mpph21/Proyecto-Byul/b-max.jpg

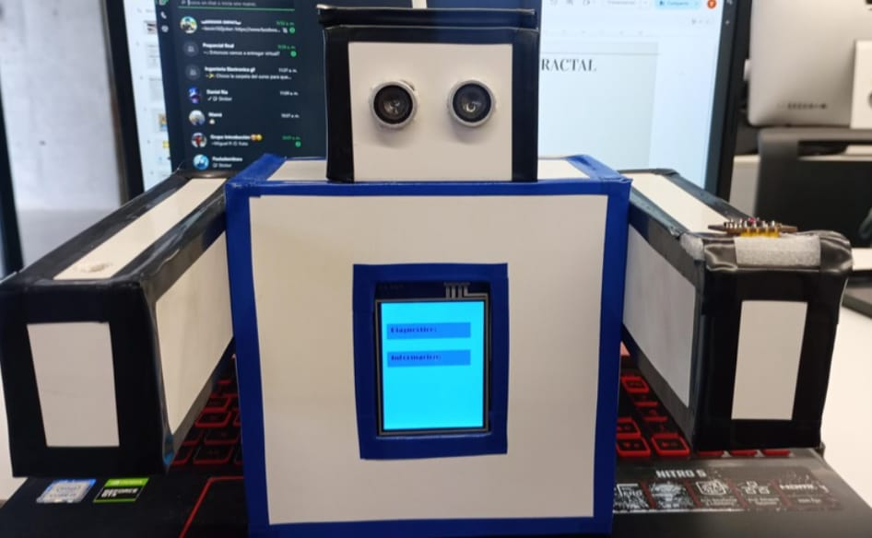
b-max.jpg
