mpph21/Proyecto-Byul/cronograma.png

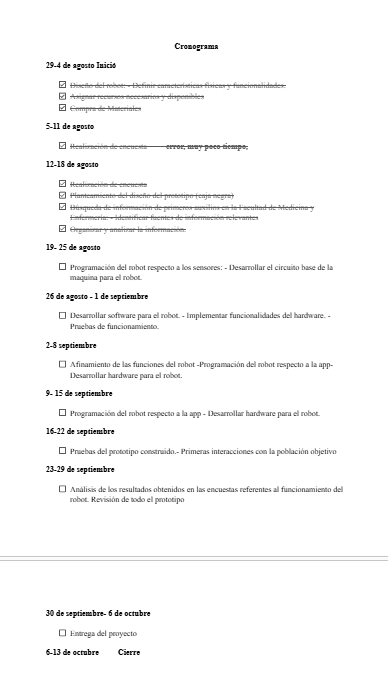
cronograma.png
