mpph21/Proyecto-Byul/diagrama .png

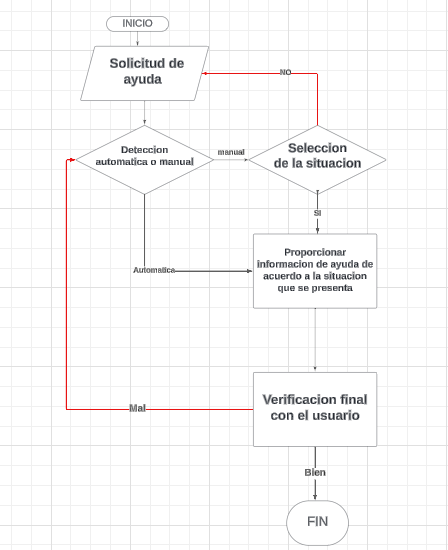
diagrama .png
