mpph21/Proyecto-Byul/Diagrama de interacion .png

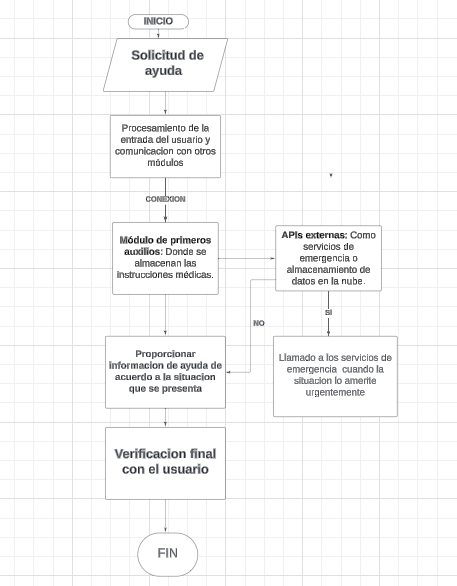
Diagrama de interacion .png
