mpph21/Proyecto-Byul/diagrama_de_caja_negra.jpg

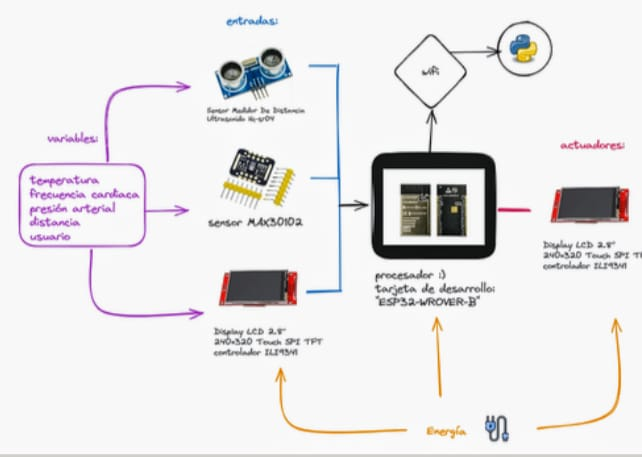
diagrama_de_caja_negra.jpg
