mpph21/Proyecto-Byul/interconectados.jpg

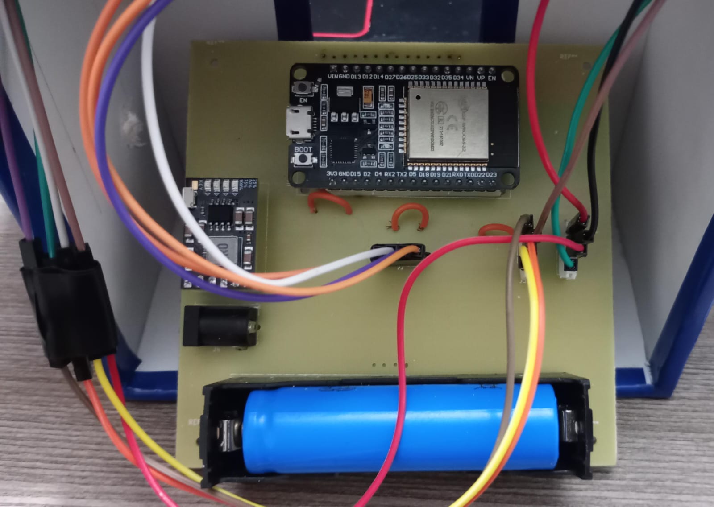
interconectados.jpg
