mpph21/Proyecto-Byul/pantallaLCD. .jpg

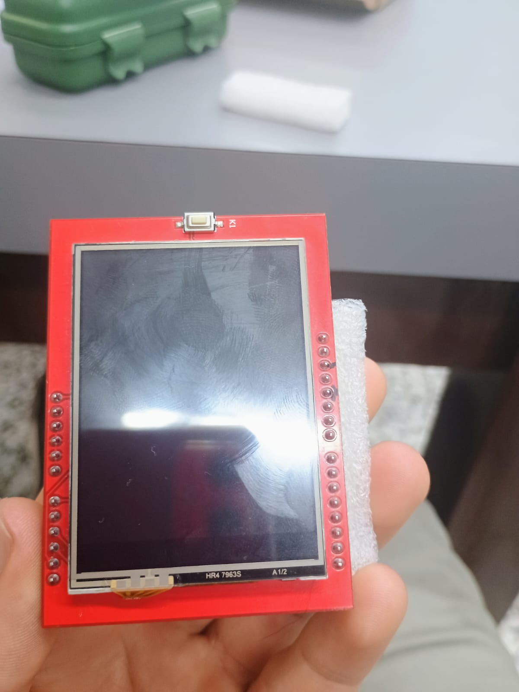
pantallaLCD. .jpg
