mpph21/Proyecto-Byul/pcbByul/Imagen de WhatsApp 2024-09-24 a las 17.16.44_98278a7d.jpg

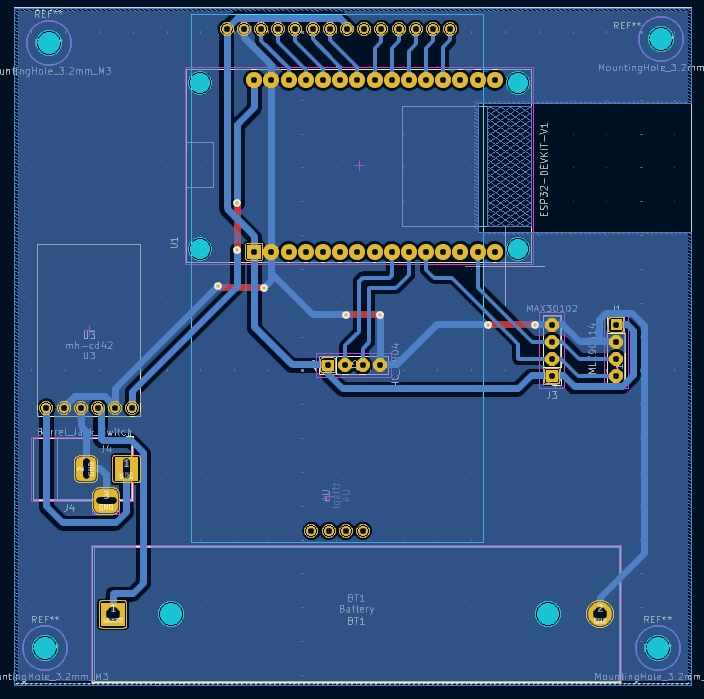
pcbByul/Imagen de WhatsApp 2024-09-24 a las 17.16.44_98278a7d.jpg
