mpph21/Proyecto-Byul/pcbByul/Imagen de WhatsApp 2024-09-24 a las 17.17.50_aacd6478.jpg

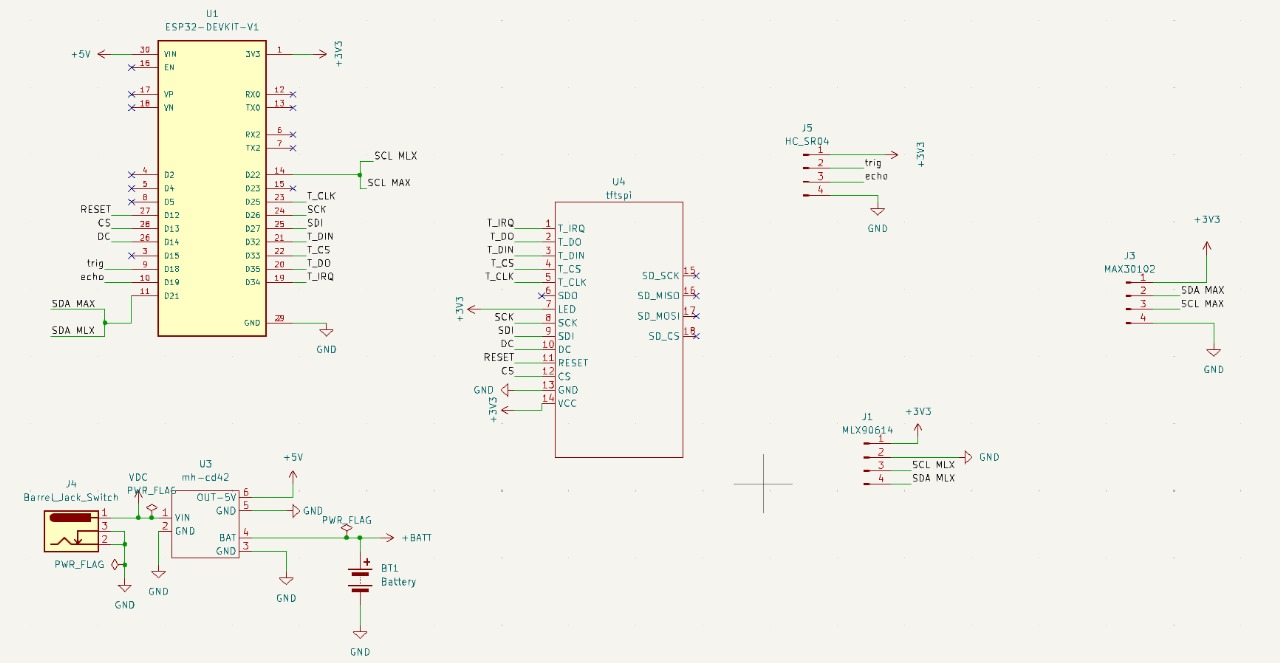
pcbByul/Imagen de WhatsApp 2024-09-24 a las 17.17.50_aacd6478.jpg
