mpph21/Proyecto-Byul/pcbByul/Imagen de WhatsApp 2024-09-24 a las 17.18.33_b2b94559.jpg

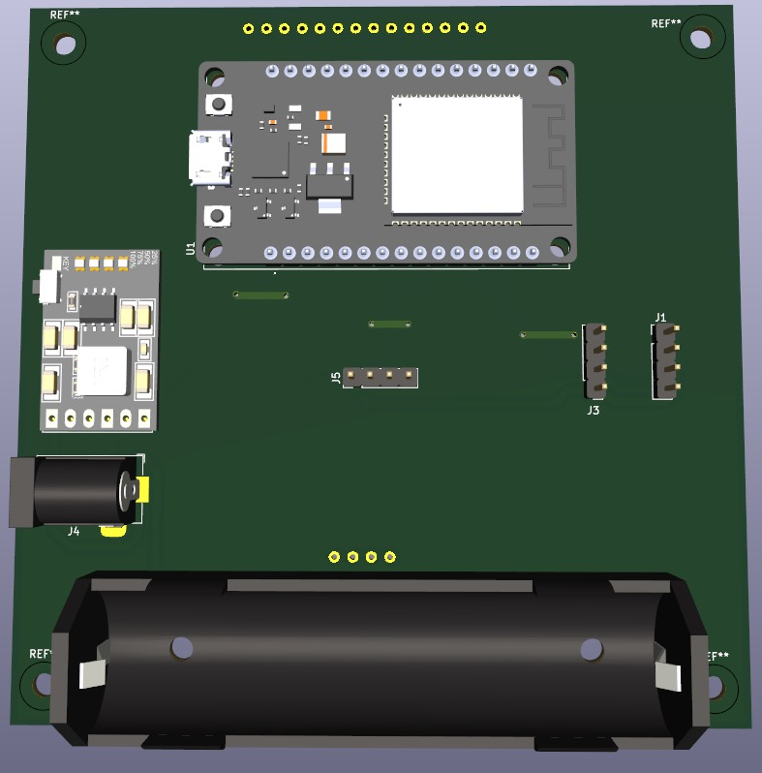
pcbByul/Imagen de WhatsApp 2024-09-24 a las 17.18.33_b2b94559.jpg
