mpph21/Proyecto-Byul/pcbByul/Imagen de WhatsApp 2024-09-24 a las 17.18.48_08502464.jpg

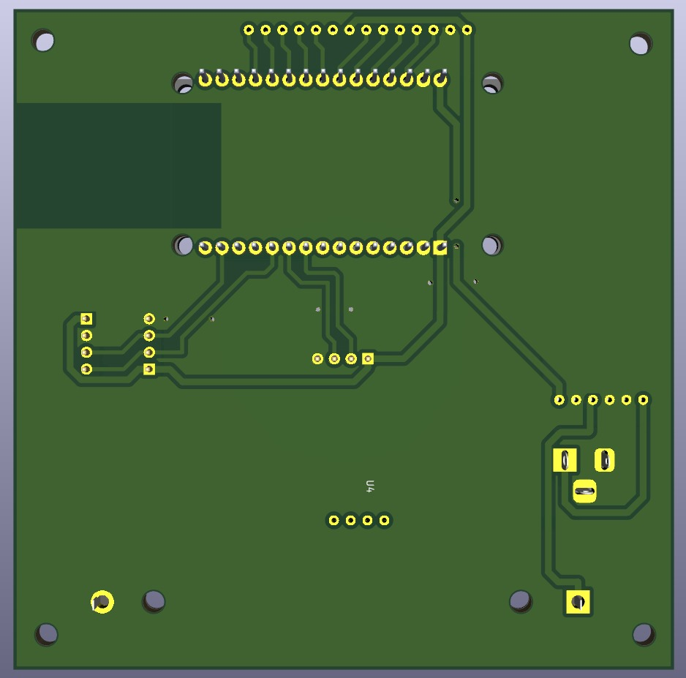
pcbByul/Imagen de WhatsApp 2024-09-24 a las 17.18.48_08502464.jpg
