mpph21/Proyecto-Byul/Planeación Byul/Diagrama_projecto_nacho.png

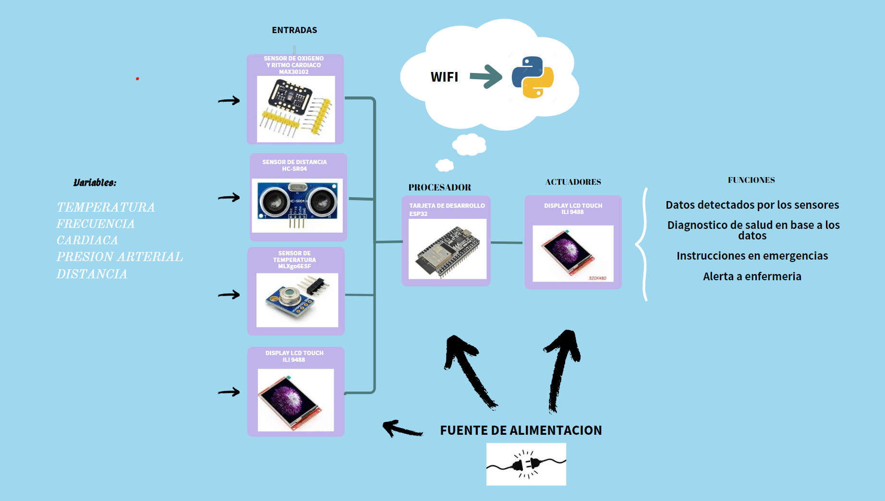
Planeación Byul/Diagrama_projecto_nacho.png
