mpph21/Proyecto-Byul/robot.jpg

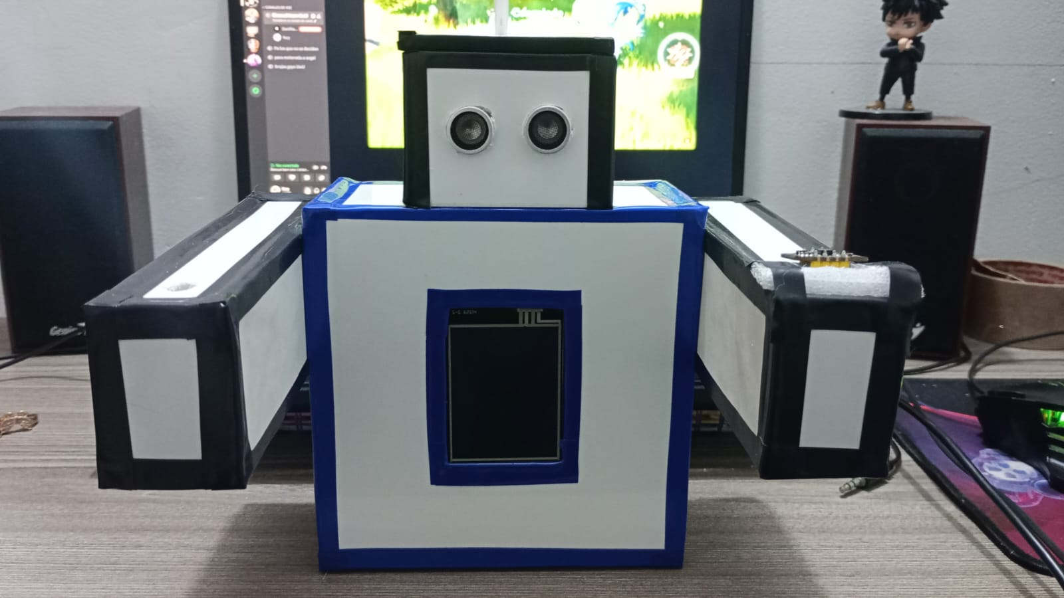
robot.jpg
