mpph21/Proyecto-Byul/Sistemas_subsistemas.jpg

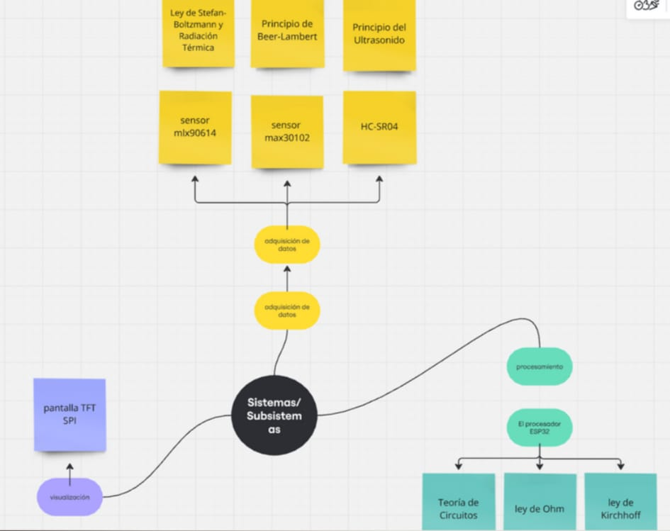
Sistemas_subsistemas.jpg
