mpph21/Proyecto-Byul/Planeación Byul/InvestigacionComponentes/ili9341-module.png

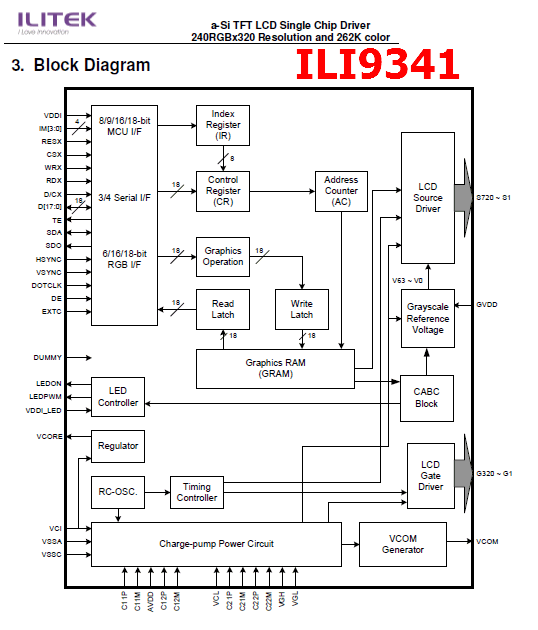
Planeación Byul/InvestigacionComponentes/ili9341-module.png
