mpph21/Proyecto-Byul/Planeación Byul/InvestigacionComponentes/OIP.png

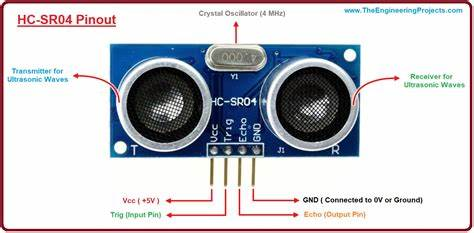
Planeación Byul/InvestigacionComponentes/OIP.png
