mpph21/Proyecto-Byul/Planeación Byul/InvestigacionComponentes/R.png

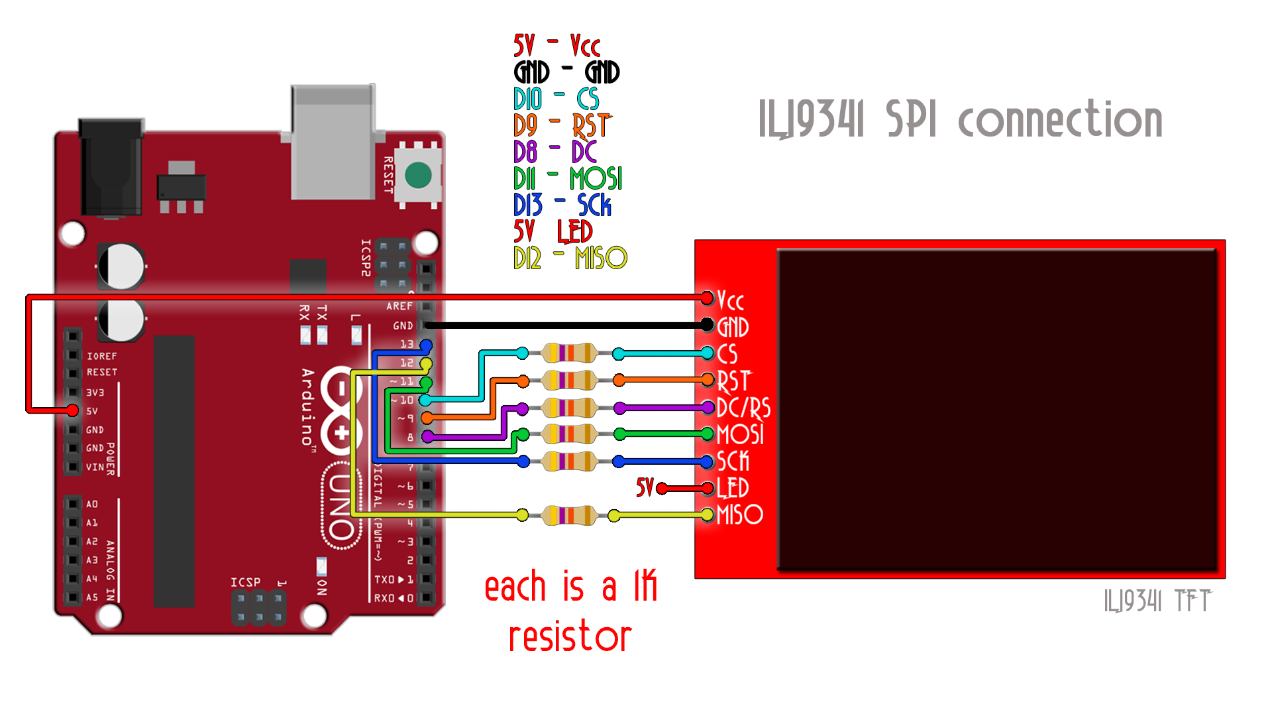
Planeación Byul/InvestigacionComponentes/R.png
