mpph21/Proyecto-Byul/Planeación Byul/InvestigacionComponentes/arduino_max30102_wiring.png

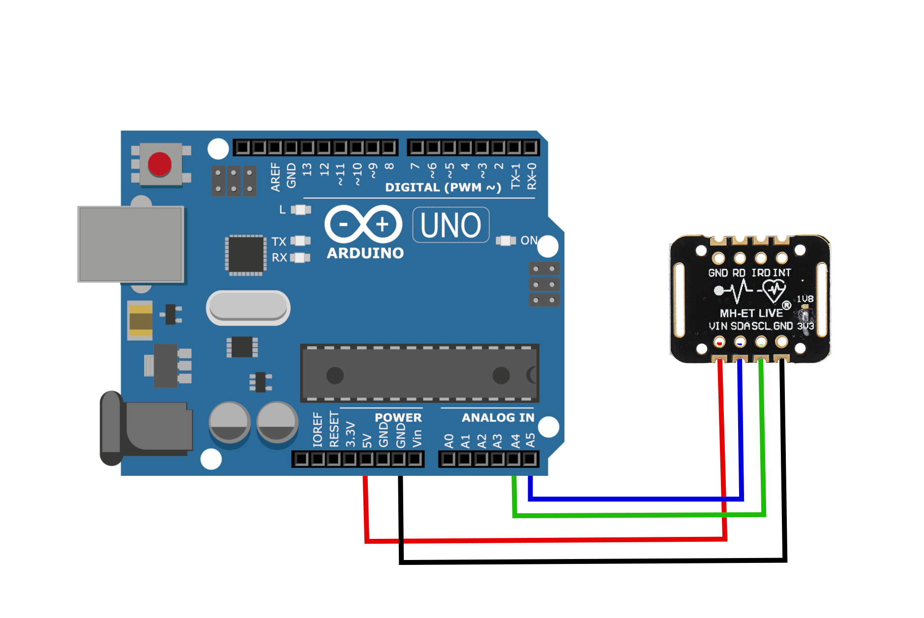
Planeación Byul/InvestigacionComponentes/arduino_max30102_wiring.png
