mpph21/Proyecto-Byul/Planeación Byul/InvestigacionComponentes/ESP8266-Ultrasonic-Sensor-Wiring-Fritzing-Diagram.png

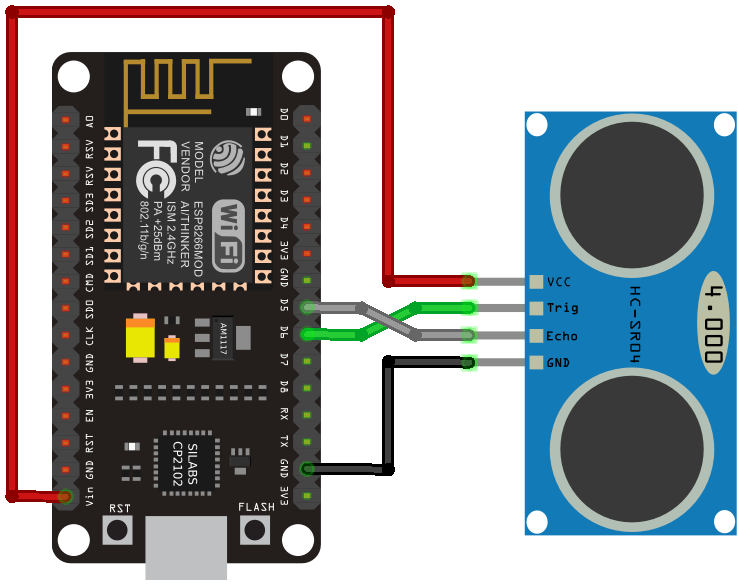
Planeación Byul/InvestigacionComponentes/ESP8266-Ultrasonic-Sensor-Wiring-Fritzing-Diagram.png
