mpph21/Proyecto-Byul/Planeación Byul/InvestigacionComponentes/wiring-diagram.png

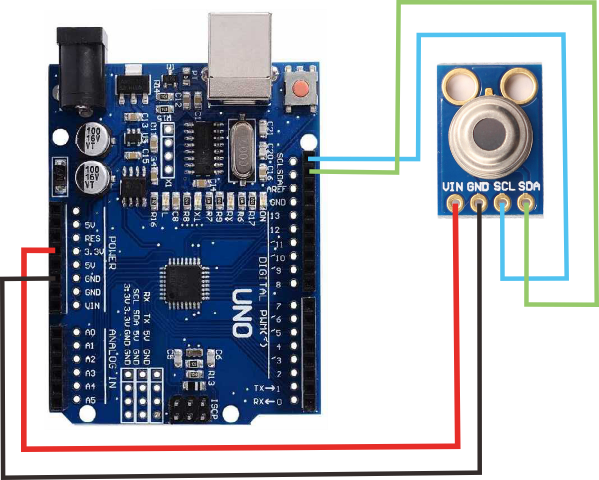
Planeación Byul/InvestigacionComponentes/wiring-diagram.png
