mpph21/Proyecto-Byul/ByulCodigo/codigoFinal/auxInfo.py

steps = [
            "Vendaje de Heridas:\n\nVendas: sirven para inmovilizar extremidades y realizar compresion en caso de hemorragias. Pueden ser elasticas, de tela o de gasa.\n\nHerida: Lesion, normalmente sangrante, que se produce en los tejidos, exteriores del cuerpo.",
            "Paso 1. Coloque un vendaje sobre la herida\n\n - Use guantes u otra proteccion para evitar el contacto con la sangre de la persona afectada.\n\n - Limpie la herida con agua o suero fisiologico.\n\n Coloque una compresa limpia sobre toda la herida. Las compresas de gasa permiten que pase el aire y, de esta manera, la herida sana mas rapido.\n\n- Si la sangre pasa a traves de la compresa, coloque otra compresa sobre la primera.",
            "Paso 2. Cubra el vendaje\n\n- Use un rollo de gasa o tiras de tela para envolver el aposito (material utilizado para cubrir y proteger la herida) y el area alrededor de la herida varias veces.\n\n - Extienda el vendaje por lo menos una pulgada mas a cada lado del aposito.\n\n- No coloque el vendaje tan apretado que interfiera con la circulacion de la sangre a los tejidos sanos.",
            "Paso 3. Asegure el vendaje\n\n- Coloque una cinta adhesiva sobre el vendaje.\n\n- No asegure el vendaje tan apretado que el color de los dedos de las manos o de los pies se vuelve palido o azul.",
            "Paso 4. Examine la circulacion\n\n- Revise la circulacion en el area debajo del vendaje despues de varios minutos y una vez mas despues de varias horas. Si la circulacion no es buena, la piel puede verse palida o de color azul o puede sentirse fria. Los signos de una mala circulacion tambien incluyen adormecimiento y hormigueo.\n\n- Si la circulacion se redujo, afloje el vendaje de inmediato. Si los sintomas persisten, solicite atencion medica.",
            "Que no hacer:\n\n- Nunca frotar la herida para quitar la suciedad."
        ]
emergency_steps = [
            "Numeros de Emergencia:\n\nLinea 125/123 - Bogota\n\nLinea telefonica gratuita atendida por la Secretaria Distrital de Salud de Bogota, creada para responder de forma inmediata a las urgencias, emergencias y desastres relacionados con atencion en salud que ocurran en la ciudad.",
            "La linea 125/123 es manejada por personas entrenadas con espiritu de ayuda, amabilidad y cortesia, que entienden la situacion y la saben manejar. Estan capacitadas para dar una respuesta especializada e inmediata a cada solicitud.",
            "!Salve una vida, llame al 125/123!\n\nAl llamar a la linea de emergencias 125/123, proporcione la siguiente informacion precisa:\n\n1. Nombre\n2. El numero del telefono de donde esta llamando\n3. El lugar del evento: direccion correcta y orientaciones para que se pueda llegar rapidamente",
            "4. Que pasa: numero de personas afectadas, tipo de incidente y si hay alguna persona capacitada que este prestando ayuda\n5. La hora en que se presento el incidente"
        ]
        
hemorrhage_steps = [
            "Control de hemorragias:\n\na. Informacion general: Ciertas heridas, cortes, desgarros y otras lesiones pueden causar un sangrado intenso. Una persona que tiene un sangrado incontrolable puede morir en cinco minutos, por lo que es importante detener rapidamente la perdida de sangre.",
            "b. Tratamiento. En caso de sangrado intenso, toma estas medidas de primeros auxilios:\n\n1. Antes de buscar donde se encuentra la herida, ponte guantes desechables y equipo de proteccion personal, si lo tienes.\n\n2. Quita cualquier tipo de ropa o suciedad sobre la herida. Busca el origen del sangrado. Es posible que la persona haya sufrido mas de una lesion. Quita cualquier suciedad evidente de la herida, pero no intentes limpiarla.",
            "3. Deten el sangrado. Cubre la herida con una gasa esteril o un paño limpio. Presiona firmemente con la palma de la mano hasta que deje de sangrar. Envuelve la herida con una venda gruesa o un pano limpio y cinta adhesiva. Eleva la zona de la herida por encima de la altura del corazon, en la medida de lo posible.",
            "4. Ayuda a la persona herida a recostarse. Si es posible, coloca a la persona sobre una alfombra o una manta para evitar que pierda calor corporal. Eleva los pies si notas signos de estado de choque, como debilidad, piel seca y sudorosa o pulso acelerado. Tranquiliza a la persona herida.",
            "5. Coloca mas vendas si es necesario. Si la sangre se filtra a traves de la venda, coloca mas gasa o panos encima. Luego, sigue presionando con firmeza la zona.",
            "6. Torniquetes: un torniquete controla eficazmente un sangrado en una extremidad que pone en riesgo la vida. De ser necesario, aplica un torniquete comprado, si lo tienes y sabes como usarlo. Cuando llegue el personal de ayuda, informales el tiempo que lleva colocado el torniquete.",
            "7. Manten a la persona inmovil. Si estas esperando a que llegue el personal de ayuda, intenta que la persona herida no se mueva. Si no has llamado al personal de ayuda, lleva a la persona a la sala de emergencias lo antes posible.",
            "8. Lavate las manos. Despues de ayudar a la persona herida, lavate las manos, aunque no parezca que te hayas manchado con sangre.",
            "c. Que evitar:\n\n1. No quites objetos grandes o que esten muy incrustados.\n2. No explores la herida.\n3. No apliques presion sobre una lesion en el ojo ni un objeto incrustado.\n4. No apliques presion sobre una herida en la cabeza si sospechas que hay una fractura de craneo.\n5. No uses un torniquete improvisado, como una bufanda o un cinturon."
        ]
        
burn_steps = [
            "QUEMADURAS MENORES:\n"
            "Si no hay rupturas en la piel:\n"
            "Deje correr agua fria sobre la zona de la quemadura o sumerja la zona en agua fria (no helada).\n"
            "Mantenga la zona en el agua durante al menos de 5 a 30 minutos. Una toalla limpia, humeda y fria tambien ayuda a reducir el dolor.\n"
            "Calme y reconforte a la persona.\n"
            "Luegodelavar o remojar la quemadura en agua, cubrala con un vendaje esteril y seco o con un aposito limpio.\n"
            "Proteja la quemadura de presiones o fricciones.\n"
            "El ibuprofeno o el paracetamol de venta libre pueden ayudar a aliviar el dolor y la inflamacion. NO le de acido acetilsalicilico (aspirin) a ninos menores de 12 años.\n"
            "Una vez que se enfrie la piel, una locion humectante que contenga aloe y un antibiotico tambien puede ayudar.\n"
            "Las quemaduras menores suelen sanar sin tratamiento adicional.\n"
            "Asegurese que la persona este al dia con la vacuna antitetanica.",

            "QUEMADURAS GRAVES:\n"
            "Si alguien se prende fuego, digale que se detenga, se tire al suelo y ruede.\n"
            "Envuelva a la persona con un material grueso como un abrigo de algodon o lana, una alfombra o una manta.\n"
            "Rocie agua sobre la persona.\n"
            "Cerciorese de que la persona ya no este en contacto con materiales ardientes o humeantes.\n"
            "NO le quite las ropas quemadas que esten pegadas a la piel.\n"
            "Verifique que la persona este respirando. De ser necesario, comience a administrar respiracion artificial y RCP.\n"
            "Cubra la zona de la quemadura con un vendaje esteril y seco o una tela limpia.\n"
            "Si los dedos de las manos o de los pies sufrieron quemaduras, separelos con compresas secas.\n"
            "Eleve la parte del cuerpo quemada por encima del nivel del corazon.\n"
            "NO toque directamente a la victima si una lesion electrica causo la quemadura.",
            
            "Las cosas que NO se deben hacer para las quemaduras incluyen:\n"
            "NO aplique aceite, mantequilla, hielo, medicamentos, cremas, aceites en aerosol ni ningun otro remedio casero en las quemaduras graves.\n"
            "NO respire, sople ni tosa sobre la quemadura.\n"
            "NO toque la piel muerta o ampollada.\n"
            "NO retire la ropa que este pegada a la piel.\n"
            "NO administre nada a la persona por via oral si hay una quemadura grave.\n"
            "NO ponga una quemadura grave en agua fria, pues esto puede causar shock.\n"
            "NO coloque una almohada debajo de la cabeza de la persona si hay quemaduras de la via respiratoria, esto puede cerrarla."
        ]

exploration_steps = [
            "Secuencia en la exploracion primaria de una victima:\n"
            "En cualquier tipo de accidente se debe en un principio activar el sistema de emergencia que esta conformado por tres acciones para atender a la victima:\n"
            "1. Proteger: Antes de actuar, lo primero que debemos hacer es identificar que tanto nosotros, como el afectado no estemos en una situacion de riesgo.\n"
            "2. Avisar: Tan pronto sea posible contactar a los servicios de emergencia.\n"
            "3. Socorrer: Ya habiendo protegido y avisado, se procedera a actuar sobre la victima, efectuando una evaluacion primaria y luego una secundaria.\n\n"
            "Evaluacion primaria:\n"
            "a. Reconocimiento de signos vitales:\n"
            "1. Conciencia: Para saber si la victima tiene conciencia, en primera instancia le preguntamos que le ha ocurrido. En caso de que no conteste, provocaremos un estimulo ligeramente doloroso como un pellizco; si la victima no reacciona ante este estimulo, significa que esta inconsciente. Inmediatamente y en lo posible sin tocarla, comprobaremos su respiracion.\n"
            "2. Respiracion: Para comprobar la respiracion de la victima, acercaremos la mejilla o el dorso de la mano a la boca-nariz de la victima, mirando el pecho. Podremos observar el movimiento toracico, escuchar la salida del aire y notar en la mejilla el calor del aire exhalado.\n"
            "a. Si respira: No se seguira evaluando signos vitales. Si no es un accidente traumatico, se colocara a la persona en posicion lateral.\n"
            "b. No respira: Pondremos a la victima en posicion decubito supino (estirado mirando hacia arriba). Despues, exploraremos su boca para comprobar la existencia de cuerpos extranos y procederemos a abrir las vias aereas mediante una hiperextension del cuello con la maniobra de frente-menton, evitando que la lengua obstruya la via de entrada de aire. En ocasiones, con esta simple maniobra, el paciente vuelve a respirar. En caso contrario, el paro es evidente, por lo que deberemos suplir la funcion ausente mediante la respiracion artificial metodo BOCA-BOCA.\n"
            "3. Pulso: Cuando el paro respiratorio esta instaurado y ya hemos procedido a iniciar el BOCA-BOCA, es necesario comprobar el funcionamiento cardiaco mediante la toma del pulso carotideo (cuello), por ser este el mas proximo al corazon y el de mas facil localizacion. En caso de existir PULSO seguiremos efectuando la respiracion artificial, pero en el momento en que desaparezca este pulso deberemos iniciar sin demora el MASAJE CARDIACO EXTERNO, acompanado siempre de la respiracion BOCA-BOCA."
        ]

choking_steps = [
            "Atoramiento u Obstruccion de la Via Aerea por Cuerpo Extrano\n"
            "Descripcion: El atoramiento por un cuerpo extrano puede ser una emergencia que pone en peligro la vida, especialmente en ninos menores de 5 anos (con juguetes, dulces, etc.) y en adultos (con alimentos, protesis dentales, etc.). Los signos de atoramiento incluyen la senal de manos en el cuello y dificultad para respirar.\n\n"
            "Tipos de Obstruccion:\n\n"
            "Leve:\n"
            "La persona puede toser y esta consciente.\n"
            "Apoyala para que continue tosiendo.\n\n"
            "Severa:\n"
            "La persona no puede toser ni respirar.\n"
            "Solo se debe realizar la maniobra de Heimlich en personas conscientes.\n\n"
            "Maniobra de Heimlich en Adultos Conscientes:\n"
            "1. Situarse detras de la victima y rodearla con los brazos.\n"
            "2. Ubicar el punto medio entre el ombligo y el esternon.\n"
            "3. Empunyar una mano y colocarla contra el abdomen.\n"
            "4. Sujetar el punio con la otra mano y realizar una presion rapida hacia arriba y adentro.\n"
            "5. Repetir hasta que el objeto sea expulsado o la persona pierda la conciencia.\n\n"
            "En Adultos Inconscientes:\n"
            "1. Colocar a la persona en el suelo con cuidado.\n"
            "2. Activar el sistema de emergencias medicas (llamar al 125/123).\n"
            "3. Iniciar maniobras de RCP (compresiones y ventilaciones).\n\n"
            "Maniobra de Desatoramiento en Bebes Conscientes:\n"
            "1. Verificar la boca del bebe y retirar el objeto si es visible.\n"
            "2. Si no es visible, voltear al bebe boca abajo y dar 5 golpes con el talon de la mano en la espalda.\n"
            "3. Voltear al bebe boca arriba y realizar 5 compresiones toracicas.\n"
            "4. Continuar hasta que el objeto sea expulsado, el bebe respire o llore, quede inconsciente, o llegue la ayuda.\n\n"
            "En Bebes Inconscientes:\n"
            "1. Activar el sistema de emergencias medicas (llamar al 125/123).\n"
            "2. Iniciar maniobras de RCP: verificar la boca, realizar 2 ventilaciones de rescate, y luego 30 compresiones toracicas.\n"
            "3. Revaluar la via aerea cada 5 ciclos o 2 minutos.\n\n"
            "Maniobra en Ninos de 1 a 8 Anos:\n"
            "1. Manejar segun el tamano del nino, similar a un bebe o un adulto.\n"
            "2. Arrodillarse para estar a la altura del nino para realizar las maniobras adecuadamente."
        ]
        
rcp_steps = [
            "La Reanimacion Cardiopulmonar (RCP) basica es un conjunto de maniobras que puedes realizar para mantener la respiracion y circulacion en una persona con paro cardiorrespiratorio. A continuacion se presenta un resumen detallado:\n\n"
            "Identificacion del Paro Cardiorrespiratorio:\n"
            "1. Ausencia de pulso y respiracion.\n"
            "2. Piel palida, fria, y a veces azulada.\n"
            "3. Perdida de la conciencia.\n"
            "4. Inmovilidad y falta de respuesta a estimulos.\n\n"
            "Accion inicial: Si la persona esta inconsciente, activa el sistema de emergencias medicas (llama al 125 o 123) y comienza la RCP siguiendo estos pasos:\n\n"
            "Apertura de la Via Aerea:\n"
            "1. Extiende la cabeza hacia atras y eleva el menton. En ninos, coloca una almohadilla debajo de los omoplatos.\n"
            "2. Revisa la boca para eliminar objetos visibles que obstruyan la respiracion.\n\n"
            "Ventilacion:\n"
            "1. Evalua durante 10 segundos usando la tecnica MES:\n"
            "   - Mira si hay movimientos del torax y abdomen.\n"
            "   - Escucha la entrada y salida de aire.\n"
            "   - Siente el aire en tu mejilla.\n"
            "2. Si no respira, realiza respiracion boca a boca:\n"
            "   - Cubre la boca de la victima con la tuya y ventila 2 veces, asegurando expansion toracica.\n"
            "3. En caso de que este respirando pero inconsciente, colocala en la posicion de recuperacion.\n\n"
            "Circulacion: Compresiones Toracicas en Adultos:\n"
            "1. Ubica el centro del esternon: Entre las dos tetillas.\n"
            "2. Coloca el talon de una mano en el centro y entrelaza los dedos de ambas manos sin tocar el torax.\n"
            "3. Realiza compresiones: Empuja el esternon hacia abajo 3-5 cm con los brazos rectos. Permite que regrese a su posicion inicial.\n\n"
            "Ciclo de RCP:\n"
            "1. 30 compresiones seguidas de 2 ventilaciones.\n"
            "2. Realiza 5 ciclos en 2 minutos.\n"
            "3. Continua hasta que llegue ayuda, te canses, o la persona recupere la conciencia.\n\n"
            "Resumen:\n"
            "1. Cada ciclo: 30 compresiones y 2 ventilaciones.\n"
            "2. Realiza 5 ciclos en 2 minutos.\n"
            "3. Frecuencia objetivo: 100 compresiones por minuto."
        ]
